Djamal-UK/GBCCAT/media/Super_Mario_Bros._Deluxe_GBC_ScreenShot1.jpg

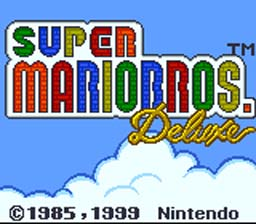
media/Super_Mario_Bros._Deluxe_GBC_ScreenShot1.jpg
